starwell19/FerroWave/3D print files/Stl/Power switch.stl

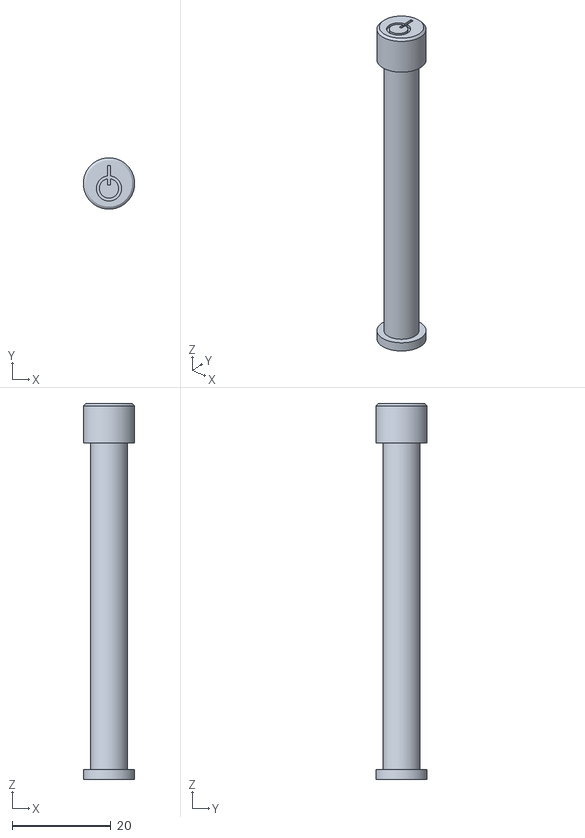
[picture p15: CAD file, 2025-12-14]
3D print files/Stl/Power switch.stl
10.4 x 10.4 x 76.0
